microphonon/acoustic-leak-detector/images/image5.jpg

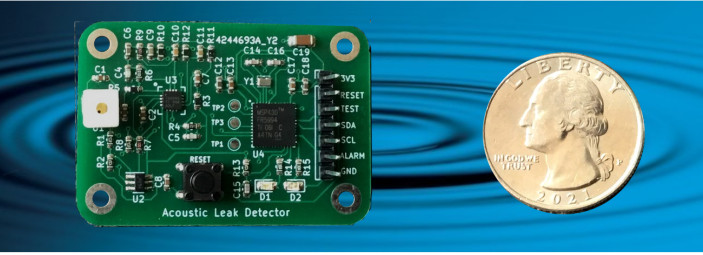
images/image5.jpg
