microphonon/acoustic-leak-detector/images/image7.jpg

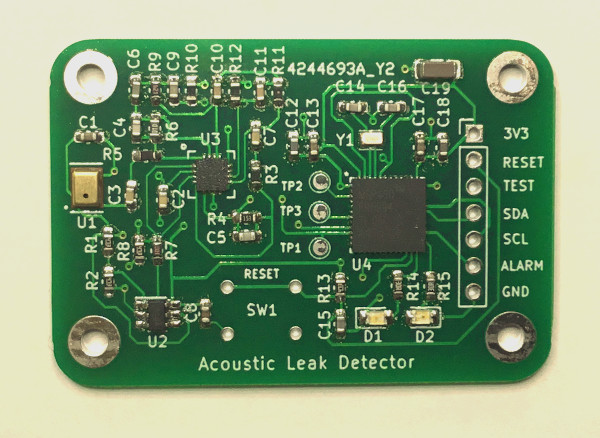
images/image7.jpg
