microphonon/acoustic-leak-detector/images/image9.jpg

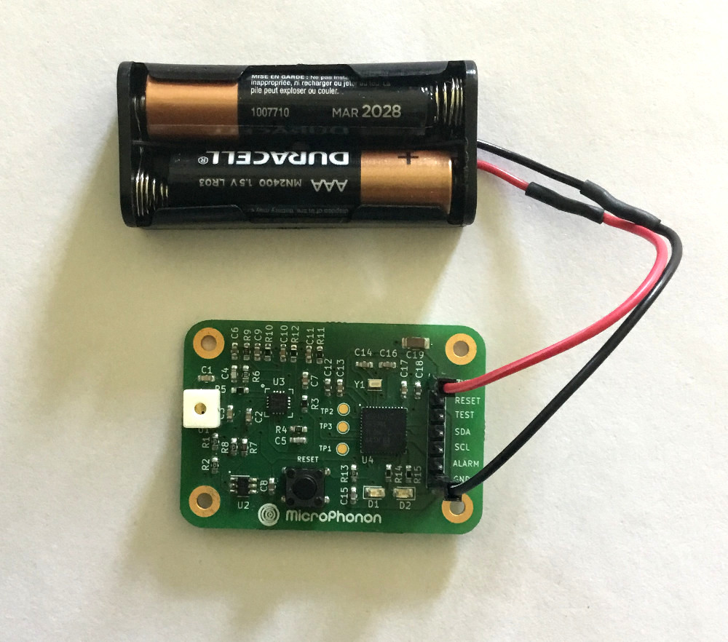
images/image9.jpg
